scottrcarlson/dsc-v3/ble_gatt_base.py

#!/usr/bin/env python

import dbus
import dbus.exceptions
import dbus.service

BLUEZ_SERVICE_NAME = 'org.bluez'
GATT_MANAGER_IFACE = 'org.bluez.GattManager1'
DBUS_OM_IFACE =      'org.freedesktop.DBus.ObjectManager'
DBUS_PROP_IFACE =    'org.freedesktop.DBus.Properties'

GATT_SERVICE_IFACE = 'org.bluez.GattService1'
GATT_CHRC_IFACE =    'org.bluez.GattCharacteristic1'
GATT_DESC_IFACE =    'org.bluez.GattDescriptor1'


class InvalidArgsException(dbus.exceptions.DBusException):
    _dbus_error_name = 'org.freedesktop.DBus.Error.InvalidArgs'


class NotSupportedException(dbus.exceptions.DBusException):
    _dbus_error_name = 'org.bluez.Error.NotSupported'


class NotPermittedException(dbus.exceptions.DBusException):
    _dbus_error_name = 'org.bluez.Error.NotPermitted'


class InvalidValueLengthException(dbus.exceptions.DBusException):
    _dbus_error_name = 'org.bluez.Error.InvalidValueLength'


class FailedException(dbus.exceptions.DBusException):
    _dbus_error_name = 'org.bluez.Error.Failed'


class Service(dbus.service.Object):
    """
    org.bluez.GattService1 interface implementation
    """
    PATH_BASE = '/org/bluez/example/service'

    def __init__(self, bus, index, uuid, primary):
        self.path = self.PATH_BASE + str(index)
        self.bus = bus
        self.uuid = uuid
        self.primary = primary
        self.characteristics = []
        dbus.service.Object.__init__(self, bus, self.path)

    def get_properties(self):
        return {
                GATT_SERVICE_IFACE: {
                        'UUID': self.uuid,
                        'Primary': self.primary,
                        'Characteristics': dbus.Array(
                                self.get_characteristic_paths(),
                                signature='o')
                }
        }

    def get_path(self):
        return dbus.ObjectPath(self.path)

    def add_characteristic(self, characteristic):
        self.characteristics.append(characteristic)

    def get_characteristic_paths(self):
        result = []
        for chrc in self.characteristics:
            result.append(chrc.get_path())
        return result

    def get_characteristics(self):
        return self.characteristics

    @dbus.service.method(DBUS_PROP_IFACE,
                         in_signature='s',
                         out_signature='a{sv}')
    def GetAll(self, interface):
        if interface != GATT_SERVICE_IFACE:
            raise InvalidArgsException()

        return self.get_properties()[GATT_SERVICE_IFACE]


class Characteristic(dbus.service.Object):
    """
    org.bluez.GattCharacteristic1 interface implementation
    """
    def __init__(self, bus, index, uuid, flags, service):
        self.path = service.path + '/char' + str(index)
        self.bus = bus
        self.uuid = uuid
        self.service = service
        self.flags = flags
        self.descriptors = []
        dbus.service.Object.__init__(self, bus, self.path)

    def get_properties(self):
        return {
                GATT_CHRC_IFACE: {
                        'Service': self.service.get_path(),
                        'UUID': self.uuid,
                        'Flags': self.flags,
                        'Descriptors': dbus.Array(
                                self.get_descriptor_paths(),
                                signature='o')
                }
        }

    def get_path(self):
        return dbus.ObjectPath(self.path)

    def add_descriptor(self, descriptor):
        self.descriptors.append(descriptor)

    def get_descriptor_paths(self):
        result = []
        for desc in self.descriptors:
            result.append(desc.get_path())
        return result

    def get_descriptors(self):
        return self.descriptors

    @dbus.service.method(DBUS_PROP_IFACE,
                         in_signature='s',
                         out_signature='a{sv}')
    def GetAll(self, interface):
        if interface != GATT_CHRC_IFACE:
            raise InvalidArgsException()

        return self.get_properties()[GATT_CHRC_IFACE]

    @dbus.service.method(GATT_CHRC_IFACE,
                        in_signature='a{sv}',
                        out_signature='ay')
    def ReadValue(self, options):
        print('Default ReadValue called, returning error')
        raise NotSupportedException()

    @dbus.service.method(GATT_CHRC_IFACE, in_signature='aya{sv}')
    def WriteValue(self, value, options):
        print('Default WriteValue called, returning error')
        raise NotSupportedException()

    @dbus.service.method(GATT_CHRC_IFACE)
    def StartNotify(self):
        print('Default StartNotify called, returning error')
        raise NotSupportedException()

    @dbus.service.method(GATT_CHRC_IFACE)
    def StopNotify(self):
        print('Default StopNotify called, returning error')
        raise NotSupportedException()

    @dbus.service.signal(DBUS_PROP_IFACE,
                         signature='sa{sv}as')
    def PropertiesChanged(self, interface, changed, invalidated):
        pass


class Descriptor(dbus.service.Object):
    """
    org.bluez.GattDescriptor1 interface implementation
    """
    def __init__(self, bus, index, uuid, flags, characteristic):
        self.path = characteristic.path + '/desc' + str(index)
        self.bus = bus
        self.uuid = uuid
        self.flags = flags
        self.chrc = characteristic
        dbus.service.Object.__init__(self, bus, self.path)

    def get_properties(self):
        return {
                GATT_DESC_IFACE: {
                        'Characteristic': self.chrc.get_path(),
                        'UUID': self.uuid,
                        'Flags': self.flags,
                }
        }

    def get_path(self):
        return dbus.ObjectPath(self.path)

    @dbus.service.method(DBUS_PROP_IFACE,
                         in_signature='s',
                         out_signature='a{sv}')
    def GetAll(self, interface):
        if interface != GATT_DESC_IFACE:
            raise InvalidArgsException()

        return self.get_properties()[GATT_DESC_IFACE]

    @dbus.service.method(GATT_DESC_IFACE,
                        in_signature='a{sv}',
                        out_signature='ay')
    def ReadValue(self, options):
        print ('Default ReadValue called, returning error')
        raise NotSupportedException()

    @dbus.service.method(GATT_DESC_IFACE, in_signature='aya{sv}')
    def WriteValue(self, value, options):
        print('Default WriteValue called, returning error')
        raise NotSupportedException()


def find_adapter(bus):
    remote_om = dbus.Interface(bus.get_object(BLUEZ_SERVICE_NAME, '/'),
                               DBUS_OM_IFACE)
    objects = remote_om.GetManagedObjects()

    for o, props in objects.items():
        if GATT_MANAGER_IFACE in props.keys():
            return o

    return None
