scottrcarlson/dsc-v3/crypto.py

#!/usr/bin/env python
# ----------------------------
# --- Crypto Helper Class
# ----------------------------
import logging
from cryptography.hazmat.primitives.ciphers import Cipher, algorithms, modes
from cryptography.hazmat.backends import default_backend
from os import urandom
import pysodium

BS = 16

pad = lambda s: s + (BS - len(s) % BS) * chr(BS - len(s) % BS)
unpad = lambda s : s[:-ord(s[len(s)-1:])]

# logging.basicConfig(level=logging.DEBUG,format='%(name)-12s| %(levelname)-8s| %(message)s')


class Crypto(object):
	def __init__(self):
		self.log = logging.getLogger()
		# self.log.setLevel(logging.DEBUG)

	def encrypt(self, key, pt):
		if isinstance(pt, unicode):
			ptbytestr = pt.encode('utf-8')
		else:
			ptbytestr = pt

		key = pad(key)
		ptbytestr = pad(ptbytestr)

		iv = self.generateIV()
		cipher = Cipher(algorithms.AES(key), modes.CBC(iv), backend=default_backend())
		encryptor = cipher.encryptor()
		ct = encryptor.update(ptbytestr) + encryptor.finalize()

		return iv + ct

	def decrypt(self, key, ct):
		key = pad(key)
		iv = ct[:16]
		ct = ct[16:]
		try:
			cipher = Cipher(algorithms.AES(key), modes.CBC(iv), backend=default_backend())
			decryptor = cipher.decryptor()
			pt = decryptor.update(ct) + decryptor.finalize()
			pt = unpad(pt)
		except Exception:
			self.log.error("Failed to decrypt packet.")
			return ""

		return pt

	def generateIV(self):
		random_bytes = urandom(16)
		return random_bytes

	def encrypt_aead(self, key, pt):
		nonce = pysodium.randombytes(8)
		ad = ""
		cipher = pysodium.crypto_aead_chacha20poly1305_encrypt(pt, ad, nonce, key)
		#print "Chacha20 Poly1305: Plaintext Len: " + str(len(pt)) + " Cipher Len: " + str(len(cipher))
		return nonce + cipher

	def decrypt_aead(self, key, ct):
		nonce = ct[:8]
		cipher = ct[8:]
		ad = ""
		try:
			plaintext = pysodium.crypto_aead_chacha20poly1305_decrypt(cipher, ad, nonce, key)
		except Exception:
			self.log.error("Failed to decrypt packet.")
			return ""
					
		return plaintext
