scottrcarlson/dsc-v3/screen.py

#!/usr/bin/python
# ----------------------------
# --- DSC2 SCREEN CONSTANTS
# ----------------------------

main_menu = {
    0: "Send Msg",
    1: "View Msgs",
    2: "Status",
    3: "Network Settings",
    4: "RF Tuning Params",
    5: "Logs",
    6: "Shutdown System",
}

network_settings_menu = {
    0: "Airplane Mode:",
    1: "Total Nodes:",
    2: "TDMA Slot(0-n):",
    3: "TX Time(s):",
    4: "Deadband(s):",
}
 
rf_tuning_menu = {
    0: "Freq:",
    1: "Bandwidth:",
    2: "Spread Factor:",
    3: "Coding Rate:",
    4: "TX Power(dBm):",
    5: "Sync Word:",
}

compose_menu = {
    0: "",
    1: "ok",
    2: "yo",
    3: "Where are you?",
    4: "Where/When do you want to meet?",
    5: "I am ",
    6: "Meet you at ",
    7: "I'll be there in ",
    8: "where",
    9: "Let's grab some beers!",
}
