scottrcarlson/dsc-v3/ui.py

#!/usr/bin/python
# ----------------------------
# --- DSC3 UI THREAD
# ----------------------------
import time
import RPi.GPIO as GPIO
import iodef
from threading import *
import os
import screen as scr
import logging
import subprocess

# DISPLAY MODES
m_IDLE = 0
m_SETTINGS = 1
m_SPLASH = 2
m_LOG_VIEWER = 3
m_COMPOSE_MENU = 4
m_COMPOSE = 5
m_MAIN_MENU = 6
m_DIALOG = 7
m_MSG_VIEWER = 8
m_DIALOG_YESNO = 9
m_DIALOG_TASK = 11
m_REG = 12
m_STATUS = 13
m_RF_TUNING = 14
m_LOCK = 15

# DIALOG COMMAND (If Yes is Chosen)
cmd_SHUTDOWN = 0
cmd_CLEARMSGS = 1
cmd_MANUALSYNCCLK = 2

keyboard = "abcdefghijklmnopqrstuvwxyz1234567890!?$%.-"


class UI(Thread):
    def __init__(self, display, message, crypto, radio, config, heartbeat):
        Thread.__init__(self)
        self.event = Event()
        self.log = logging.getLogger()
        # self.log.setLevel(logging.INFO)

        self.heartbeat = heartbeat

        self.active_high = True
        bounce_time = 80
        if config.hw_rev != 1:
            bounce_time = 175  # HW Rev2 has no hardware debouncing
            self.active_high = False

        GPIO.add_event_detect(iodef.PIN_KEY_UP, GPIO.FALLING, callback=self.key_up, bouncetime=bounce_time)
        GPIO.add_event_detect(iodef.PIN_KEY_DOWN, GPIO.FALLING, callback=self.key_down, bouncetime=bounce_time)
        GPIO.add_event_detect(iodef.PIN_KEY_LEFT, GPIO.FALLING, callback=self.key_left, bouncetime=bounce_time)
        GPIO.add_event_detect(iodef.PIN_KEY_RIGHT, GPIO.FALLING, callback=self.key_right, bouncetime=bounce_time)
        GPIO.add_event_detect(iodef.PIN_KEY_ENTER, GPIO.FALLING, callback=self.key_enter, bouncetime=bounce_time)
        if config.hw_rev == 1:
            GPIO.add_event_detect(iodef.PIN_KEY_BACK, GPIO.RISING, callback=self.key_back, bouncetime=bounce_time)
        else:
            GPIO.add_event_detect(iodef.PIN_KEY_BACK, GPIO.FALLING, callback=self.key_back, bouncetime=bounce_time)

        self.display = display
        self.crypto = crypto
        self.message = message
        self.config = config
        self.radio = radio

        self.is_idle = False

        self.key_repeat = -1  # -1/None 0/Left 1/Right
        self.key_repeat_rate = 0.08
        self.key_repeat_delay = 0.5
        self.dialog_delay = 0
        self.lock()
        self.log.info("Initialized UI Thread.")

    def run(self):
        self.event.wait(1)
        key_repeat_time = 0
        key_delay_time = 0
        heartbeat_time = 0
        dialog_time = 0
        idle_time = 0
        while not self.event.is_set():
            try:
                

                if time.time() - heartbeat_time > 5:
                    heartbeat_time = time.time()
                    if self.heartbeat.qsize() == 0:
                        self.heartbeat.put_nowait("hb")
                elif time.time() - heartbeat_time < 0:
                        self.log.warn("Time changed to past. Re-initializing.")
                        heartbeat_time = time.time()
                if self.display.mode == m_DIALOG:
                    if dialog_time == 0:
                        dialog_time = time.time()
                    if time.time() - dialog_time > self.dialog_delay:
                        dialog_time = time.time()
                        self.display.dialog_confirmed = True
                

                try:
                    if time.time() - idle_time > 15:
                        idle_time = time.time()
                        if self.is_idle:
                            self.idle()
                            self.is_idle = False
                        else:
                            self.is_idle = True
                    elif time.time() - idle_time < 0:
                        self.log.warn("Time changed to past. Re-initializing.")
                        idle_time = time.time()
                except Exception as e:
                    self.log.error(str(e))

                if self.key_repeat == -1:
                    key_delay_time = time.time()

                if time.time() - key_repeat_time > self.key_repeat_rate:
                    key_repeat_time = time.time()
                    if time.time() - key_delay_time > self.key_repeat_delay:
                        if self.key_repeat == 1:  # Left Key Repeat
                            if GPIO.input(iodef.PIN_KEY_LEFT) == self.active_high:
                                self.display.key_repeating = True
                                self.display.col_index -= 1
                                if self.display.row_index == -1:
                                    if self.display.col_index < 0:
                                        self.display.col_index = 0
                                elif self.display.col_index < 0:
                                    self.display.col_index = 20
                                    if self.display.row_index == 1:
                                        self.display.row_index = 0
                                    else:
                                        self.display.row_index = 1
                            else:
                                self.display.key_repeating = False
                                self.key_repeat = -1
                        elif self.key_repeat == 2:  # Right Key Repeat
                            if GPIO.input(iodef.PIN_KEY_RIGHT) == self.active_high:
                                self.display.key_repeating = True
                                self.display.col_index += 1
                                if self.display.row_index == -1:
                                    if self.display.col_index > 1:
                                        self.display.col_index = 1
                                elif self.display.col_index > 20:
                                    self.display.col_index = 0
                                    if self.display.row_index == 0:
                                        self.display.row_index = 1
                                    else:
                                        self.display.row_index = 0
                            else:
                                self.display.key_repeating = False
                                self.key_repeat = -1
                elif time.time() - key_repeat_time < 0:
                        self.log.warn("Time changed to past. Re-initializing.")
                        key_repeat_time = time.time()

            except Exception as e:
                self.log.error("Exception: " + str(e))
            self.event.wait(0.05)

    def stop(self):
        self.log.info("Stopping UI Thread.")
        self.event.wait(2)
        self.event.set()

    def idle(self):
        if self.display.mode == m_LOCK:
            self.display.mode = m_IDLE
        elif self.display.mode == m_MAIN_MENU:
            self.display.mode = m_IDLE

    def lock(self):  # Lock Screen to prevent key presses in pocket.
        self.message.compose_msg = ""
        self.display.mode = m_LOCK

    def splash(self):
        self.display.mode = m_SPLASH

    def reg(self):
        self.display.mode = m_REG

    def main_menu(self):
        self.display.row_index = 0
        self.display.mode = m_MAIN_MENU

# ---------------------------------[KEY UP]-------------------------------------
    def key_up(self, channel):
        self.is_idle = False
        if self.display.mode == m_IDLE:
            self.display.mode = m_LOCK
        elif self.display.mode == m_SPLASH:
            self.reg()
        elif self.display.mode == m_COMPOSE or self.display.mode == m_REG:
            if self.display.row_index == 1:
                self.display.row_index = 0
            else:
                self.display.row_index = -1
                self.display.col_index = 0
        elif self.display.mode == m_MAIN_MENU:
            self.display.row_index -= 1
            if self.display.row_index < 0:
                self.display.row_index = 0
        elif self.display.mode == m_COMPOSE_MENU:
            self.display.row_index -= 1
            if self.display.row_index < 0:
                self.display.row_index = 0
        elif self.display.mode == m_MSG_VIEWER:
            self.display.horiz_index = 0
            self.display.horiz_reset_cnt = 0
            self.display.horiz_start_cnt = 0
            self.display.row_index -= 1
            if self.display.row_index < 0:
                self.display.row_index = 0
        elif self.display.mode == m_RF_TUNING:
            self.display.row_index -= 1
            if self.display.row_index < 0:
                self.display.row_index = 0
        elif self.display.mode == m_SETTINGS:
            self.display.row_index -= 1
            if self.display.row_index < 0:
                self.display.row_index = 0

# ---------------------------------[KEY DOWN]-------------------------------------
    def key_down(self, channel):
        self.is_idle = False
        # print "pressed DOWN Key."
        if self.display.mode == m_IDLE:
            self.display.mode = m_LOCK
        elif self.display.mode == m_SPLASH:
            self.reg()
        elif self.display.mode == m_COMPOSE:
            self.display.row_index += 1
            if self.display.row_index > 1:
                self.display.row_index = 1
        elif self.display.mode == m_REG:
            self.display.row_index += 1
            if self.display.row_index > 1:
                self.display.row_index = 1
        elif self.display.mode == m_MAIN_MENU:
            self.display.row_index += 1
            if self.display.row_index >= len(scr.main_menu):
                self.display.row_index = len(scr.main_menu) - 1
        elif self.display.mode == m_COMPOSE_MENU:
            self.display.row_index += 1
            if self.display.row_index >= len(scr.compose_menu):
                self.display.row_index = len(scr.compose_menu) - 1
        elif self.display.mode == m_MSG_VIEWER:
            self.display.horiz_index = 0
            self.display.horiz_reset_cnt = 0
            self.display.horiz_start_cnt = 0
            if len(self.message.group_cleartexts) != 0:
                self.display.row_index += 1
                if self.display.row_index >= len(self.message.group_cleartexts):
                    self.display.row_index = len(self.message.group_cleartexts) - 1
        elif self.display.mode == m_RF_TUNING:
            self.display.row_index += 1
            if self.display.row_index > 5:
                self.display.row_index = 5
        elif self.display.mode == m_SETTINGS:
            self.display.row_index += 1
            if self.display.row_index > 4:
                self.display.row_index = 4

# ---------------------------------[KEY LEFT]-------------------------------------
    def key_left(self, channel):
        self.is_idle = False
        # print "pressed LEFT Key."
        if self.display.mode == m_IDLE:
            self.display.mode = m_LOCK
        elif self.display.mode == m_SPLASH:
            self.reg()
        elif self.display.mode == m_COMPOSE or self.display.mode == m_REG:
            self.display.col_index -= 1
            if self.display.row_index == -1:
                if self.display.col_index < 0:
                    self.display.col_index = 0
            elif self.display.col_index < 0:
                self.display.col_index = 20
                if self.display.row_index == 1:
                    self.display.row_index = 0
                else:
                    self.display.row_index = 1
            self.key_repeat = 1  # Actuate Key Repeating
        elif self.display.mode == m_DIALOG_YESNO:
            self.display.col_index -= 1
            if self.display.col_index < 0:
                self.display.col_index = 0
        elif self.display.mode == m_RF_TUNING:
            if self.display.row_index == 0:
                self.config.freq -= 250000
                if self.config.freq < 902250000:
                    self.config.freq = 902250000
            if self.display.row_index == 1:
                self.config.bandwidth -= 1
                if self.config.bandwidth < 0:
                    self.config.bandwidth = 0
                self.config.update_bandwidth_eng()
            elif self.display.row_index == 2:
                self.config.spread_factor -= 1
                if self.config.spread_factor < 6:
                    self.config.spread_factor = 6
            elif self.display.row_index == 3:
                self.config.coding_rate -= 1
                if self.config.coding_rate < 1:
                    self.config.coding_rate = 1
                self.config.update_coding_rate_eng()
            elif self.display.row_index == 4:
                self.config.tx_power -= 1
                if self.config.tx_power < 11:  # LL-RXR-27
                    self.config.tx_power = 11
            elif self.display.row_index == 5:
                self.config.sync_word -= 1
                if self.config.sync_word < 0:
                    self.config.sync_word = 0
        elif self.display.mode == m_SETTINGS:
            if self.display.row_index == 0:
                self.config.airplane_mode = False
            if self.display.row_index == 1:
                self.config.tdma_total_slots -= 1
                if self.config.tdma_total_slots < 2:  # Whats the point if not at least 2?!
                    self.config.tdma_total_slots = 2
            elif self.display.row_index == 2:
                self.config.tdma_slot -= 1
                if self.config.tdma_slot < 0:
                    self.config.tdma_slot = 0
            elif self.display.row_index == 3:
                self.config.tx_time -= 1
                if self.config.tx_time < 1:
                    self.config.tx_time = 1
            elif self.display.row_index == 4:
                self.config.tx_deadband -= 1
                if self.config.tx_deadband < 1:
                    self.config.tx_deadband = 1
        elif self.display.mode == m_LOCK:
            if GPIO.input(iodef.PIN_KEY_ENTER) == self.active_high:
                self.main_menu()

# ---------------------------------[KEY RIGHT]-------------------------------------
    def key_right(self, channel):
        self.is_idle = False
        # print "pressed RIGHT Key."
        if self.display.mode == m_IDLE:
            self.display.mode = m_LOCK
        elif self.display.mode == m_SPLASH:
            self.reg()
        elif self.display.mode == m_COMPOSE or self.display.mode == m_REG:
            items = 1
            if self.display.mode == m_COMPOSE:
                items = 3
            self.display.col_index += 1
            if self.display.row_index == -1:
                if self.display.col_index > items:
                    self.display.col_index = items
            elif self.display.col_index > 20:
                self.display.col_index = 0
                if self.display.row_index == 0:
                    self.display.row_index = 1
                else:
                    self.display.row_index = 0
            self.key_repeat = 2  # Actuate Key Repeating
        elif self.display.mode == m_DIALOG_YESNO:
            self.display.col_index += 1
            if self.display.col_index > 1:
                self.display.col_index = 1
        elif self.display.mode == m_RF_TUNING:
            if self.display.row_index == 0:
                self.config.freq += 250000
                if self.config.freq > 927750000:
                    self.config.freq = 927750000
            if self.display.row_index == 1:
                self.config.bandwidth += 1
                if self.config.bandwidth > 3:
                    self.config.bandwidth = 3
                self.config.update_bandwidth_eng()
            elif self.display.row_index == 2:
                self.config.spread_factor += 1
                if self.config.spread_factor > 12:
                    self.config.spread_factor = 12
            elif self.display.row_index == 3:
                self.config.coding_rate += 1
                if self.config.coding_rate > 4:
                    self.config.coding_rate = 4
                self.config.update_coding_rate_eng()
            elif self.display.row_index == 4:
                self.config.tx_power += 1
                if self.config.tx_power > 26:  # LL-RXR-27
                    self.config.tx_power = 26
            elif self.display.row_index == 5:
                self.config.sync_word += 1
                if self.config.sync_word > 1024:
                    self.config.sync_word = 1024
        elif self.display.mode == m_SETTINGS:
            if self.display.row_index == 0:
                self.config.airplane_mode = True
            elif self.display.row_index == 1:
                self.config.tdma_total_slots += 1
            elif self.display.row_index == 2:
                self.config.tdma_slot += 1
            elif self.display.row_index == 3:
                self.config.tx_time += 1
            elif self.display.row_index == 4:
                self.config.tx_deadband += 1

# ---------------------------------[KEY ENTER]-------------------------------------
    def key_enter(self, channel):
        self.is_idle = False
        if self.display.mode == m_IDLE:
            self.display.mode = m_LOCK
        elif self.display.mode == m_SPLASH:
            self.reg()
        elif self.display.mode == m_REG:
            if self.display.row_index >= 0:
                index = (self.display.row_index * 21) + self.display.col_index
                if self.display.reg_stage == 1:
                    if len(self.config.alias) < 8:
                        self.config.alias = self.config.alias + keyboard[index:index + 1]
                elif self.display.reg_stage == 2:
                    if len(self.config.netkey) < 16:
                        self.config.netkey = self.config.netkey + keyboard[index:index + 1]
                elif self.display.reg_stage == 3:
                    if len(self.config.alias) < 16:
                        self.config.groupkey = self.config.groupkey + keyboard[index:index + 1]

            else:
                if self.display.col_index == 0:  # NEXT Field
                    self.display.reg_stage += 1
                    if self.display.reg_stage > 4:
                        self.display.reg_stage = 1

                elif self.display.col_index == 1:  # DONE. Register node.
                    if self.display.reg_stage == 4:
                        self.display.row_index = 0
                        self.display.col_index = 0
                        self.display.dialog_task_done = False
                         
                        # Pad the keys. Not a great idea. Need to improve this for lazy people.
                        # Key size has to be 16bytes

                        self.config.alias = self.config.alias.ljust(8)
                        self.config.netkey = self.config.netkey.ljust(16)
                        self.config.groupkey = self.config.groupkey.ljust(16)

                        self.config.registered = True
                        self.display.mode = m_MAIN_MENU

        elif self.display.mode == m_COMPOSE:
            if self.display.row_index >= 0:
                if len(self.message.compose_msg) < self.display.horiz_max * 3:
                    index = (self.display.row_index * 21) + self.display.col_index
                    self.message.compose_msg = self.message.compose_msg + keyboard[index:index + 1]
            else:
                if self.display.col_index == 0:
                    self.display.dialog_msg = ""
                    self.display.dialog_msg2 = ""
                    self.display.dialog_msg3 = "  Sending Message..."
                    self.message.process_inbound_packet(self.config.alias, self.message.MSG_TYPE_MESSAGE, self.message.compose_msg)
                    self.display.row_index = 0
                    self.display.col_index = 0
                    self.dialog_delay = 2
                    self.display.mode = m_DIALOG
                elif self.display.col_index == 1:
                    self.message.compose_msg += " "
                elif self.display.col_index == 2:
                    self.message.compose_msg = ""
                elif self.display.col_index == 3:
                    self.message.compose_msg = ""
                    self.main_menu()
        elif self.display.mode == m_MSG_VIEWER:
            self.log.debug("User Clear Msg Request.")
            self.display.dialog_cmd = cmd_CLEARMSGS
            self.display.dialog_msg = "Clear Messages"
            self.display.dialog_msg2 = "Are you sure?"
            self.display.col_index = 0
            self.display.dialog_next_mode = m_MSG_VIEWER
            self.display.mode = m_DIALOG_YESNO
        elif self.display.mode == m_STATUS:
            self.log.debug("User Manual Sync Clock Request.")
            self.display.dialog_cmd = cmd_MANUALSYNCCLK
            self.display.dialog_msg = "Manual Clk Sync?"
            self.display.dialog_msg2 = "Are you sure?"
            self.display.col_index = 0
            self.display.dialog_next_mode = m_MAIN_MENU
            self.display.mode = m_DIALOG_YESNO
        elif self.display.mode == m_COMPOSE_MENU:
            self.message.compose_msg = scr.compose_menu[self.display.row_index]
            self.display.row_index = 0
            self.display.col_index = 0
            self.display.mode = m_COMPOSE
        elif self.display.mode == m_MAIN_MENU:
            self.log.debug("MainMenu Selected: " + scr.main_menu[self.display.row_index])
            if self.display.row_index == 0:
                if self.config.airplane_mode:
                    self.display.dialog_msg3 = " Airplane Mode Active"
                    self.display.row_index = 0
                    self.display.col_index = 0
                    self.dialog_delay = 2
                    self.display.mode = m_DIALOG
                    self.display.dialog_next_mode = m_MAIN_MENU
                else:
                    self.display.row_index = 0
                    self.display.col_index = 0
                    self.display.mode = m_COMPOSE_MENU
            elif self.display.row_index == 1:
                self.display.row_index = 0
                self.display.col_index = 0
                self.display.dialog_next_mode = m_MAIN_MENU
                self.display.mode = m_MSG_VIEWER
            elif self.display.row_index == 2:
                self.display.mode = m_STATUS
            elif self.display.row_index == 3:
                self.display.col_index = 0
                self.display.row_index = 0
                self.display.mode = m_SETTINGS
            elif self.display.row_index == 4:
                self.display.col_index = 0
                self.display.row_index = 0
                self.display.mode = m_RF_TUNING
            elif self.display.row_index == 5:
                self.display.mode = m_LOG_VIEWER
            elif self.display.row_index == 6:
                self.display.dialog_cmd = cmd_SHUTDOWN
                self.display.dialog_msg = "Shutdown?"
                self.display.dialog_msg2 = "Are you sure?"
                self.display.col_index = 0
                self.display.mode = m_DIALOG_YESNO
        elif self.display.mode == m_DIALOG_YESNO:
            if self.display.col_index == 1:  # Yes Chosen
                if self.display.dialog_cmd == cmd_SHUTDOWN:
                    self.display.dialog_msg = "DSCv3"
                    self.display.dialog_msg2 = "Shutting Down."
                    self.display.dialog_task_done = False
                    self.display.mode = m_DIALOG_TASK
                    os.system("sudo shutdown -h now")
                elif self.display.dialog_cmd == cmd_CLEARMSGS:
                    self.message.network_plaintexts = []
                    self.display.mode = m_MSG_VIEWER
                elif self.display.dialog_cmd == cmd_MANUALSYNCCLK:
                    pipe = subprocess.Popen(
                            ["sudo", "dat12e", '-s', "07/30/17 00:00:00"],  # node is also available
                            stdout=subprocess.PIPE)
                    pipe = subprocess.Popen(
                            ["sudo", "hwclock", '-w'],  # node is also available
                            stdout=subprocess.PIPE)
                    self.display.mode = self.display.dialog_next_mode
            else:
                self.display.mode = self.display.dialog_next_mode

# ---------------------------------[KEY BACK]-------------------------------------
    def key_back(self, channel):
        self.is_idle = False
        if self.display.mode == m_IDLE:
            self.display.mode = m_LOCK
        elif self.display.mode == m_SPLASH:
            self.reg()
        elif self.display.mode == m_MAIN_MENU:
            pass
        elif self.display.mode == m_STATUS:
            # self.display.mode = m_MAIN_MENU
            self.main_menu()
        elif self.display.mode == m_COMPOSE:
            self.message.compose_msg = self.message.compose_msg[:-1]
        elif self.display.mode == m_COMPOSE_MENU:
            self.main_menu()
        elif self.display.mode == m_SETTINGS:
            self.config.save_config(True)
            self.config.req_update_network = True
            self.main_menu()
        elif self.display.mode == m_LOG_VIEWER:
            self.main_menu()
        elif self.display.mode == m_MSG_VIEWER:
            self.main_menu()
        elif self.display.mode == m_RF_TUNING:
            self.radio.set_params(self.config.freq,
                                  self.config.bandwidth,
                                  self.config.spread_factor,
                                  self.config.coding_rate,
                                  self.config.tx_power,
                                  self.config.sync_word,
                                  True)
            self.main_menu()
        elif self.display.mode == m_REG:
            if self.display.reg_stage == 1:
                if len(self.config.alias) > 0:
                    self.config.set_alias(self.config.alias[:-1])
            elif self.display.reg_stage == 2:
                if len(self.config.netkey) > 0:
                    self.config.set_netkey(self.config.netkey[:-1])
            elif self.display.reg_stage == 3:
                if len(self.config.groupkey) > 0:
                    self.config.set_groupkey(self.config.groupkey[:-1])
        elif self.display.mode == m_LOCK:
            if GPIO.input(iodef.PIN_KEY_LEFT) == self.active_high:
                self.main_menu()
        else:
            self.main_menu()
